JacSko/SmartHome_CoreApplication/sw/drivers/test/unit/uart_engine_tests.cpp

#include "gtest/gtest.h"
#ifdef __cplusplus
extern "C" {
#endif
#include "../../source/uart_engine.c"
#include "../../../../ext_lib/CMSIS/stubs/device/stm32f4xx.h"
#ifdef __cplusplus
}
#endif

#include "gpio_lib_mock.h"

/* ============================= */
/**
 * @file uart_engine_tests.cpp
 *
 * @brief Unit tests of UART engine module
 *
 * @details
 * This tests verifies behavior of UART engine module
 *
 * @author Jacek Skowronek
 * @date 01/11/2020
 */
/* ============================= */

using namespace ::testing;

struct callbackMock
{
	MOCK_METHOD1(callback, void(const char*));
};

callbackMock* callMock;

void fake_callback(const char* buf)
{
	callMock->callback(buf);
}

struct uartengineFixture : public ::testing::Test
{
	virtual void SetUp()
	{
		stm_stub_init();
		mock_gpio_init();
		callMock = new callbackMock();
	}

	virtual void TearDown()
	{
		stm_stub_deinit();
		mock_gpio_deinit();
		delete callMock;
	}
};

/**
 * @test Module initilization test
 */
TEST_F(uartengineFixture, engine_initialization)
{

	/**
	 * <b>scenario</b>: Module initialization.<br>
	 * <b>expected</b>: RCC enabled, USART2 enabled, RXNEIE set, TXEIE not set.<br>
    * ************************************************
	 */
	UARTEngine_Config cfg = {115200, 20, 15};

	EXPECT_CALL(*gpio_lib_mock, gpio_pin_cfg(_,_,_)).Times(2);

	EXPECT_EQ(RETURN_OK, uartengine_initialize(&cfg));

	EXPECT_TRUE(READ_BIT(RCC->AHB1ENR, RCC_AHB1ENR_GPIOAEN));
	EXPECT_TRUE(READ_BIT(RCC->APB1ENR, RCC_APB1ENR_USART2EN));
	EXPECT_EQ(USART2->BRR, 50000000/cfg.baudrate);
	EXPECT_TRUE(READ_BIT(USART2->CR1, USART_CR1_RXNEIE));
	EXPECT_FALSE(READ_BIT(USART2->CR1, USART_CR1_TXEIE));
	EXPECT_TRUE(stm_stub_check_irq(USART2_IRQn, 1));
	uartengine_deinitialize();
}
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
